Shine-Bright-Meow/SlimeVR-Hyperion-BMI-BNO-PCB-Case/Resources/Images/Case/Case4.png

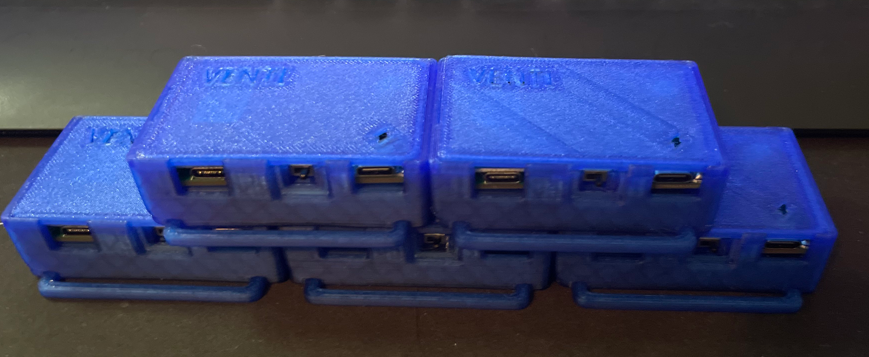
Resources/Images/Case/Case4.png
